NalaniFlynns/tiny-rmr-1-2.05/image/1.png

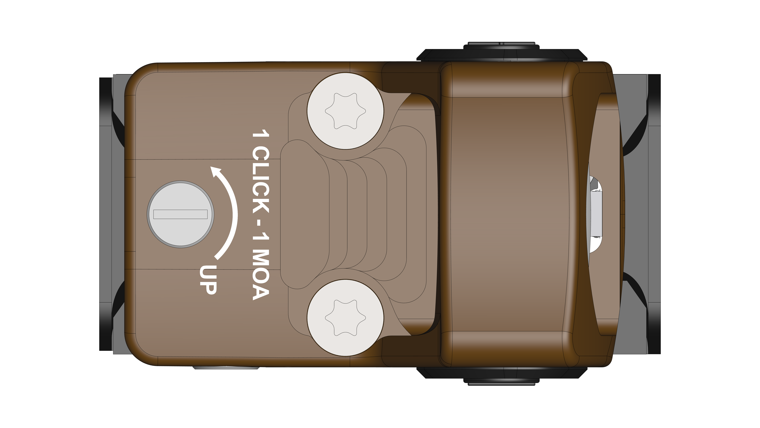
image/1.png
