NalaniFlynns/tiny-rmr-1-2.05/image/2.png

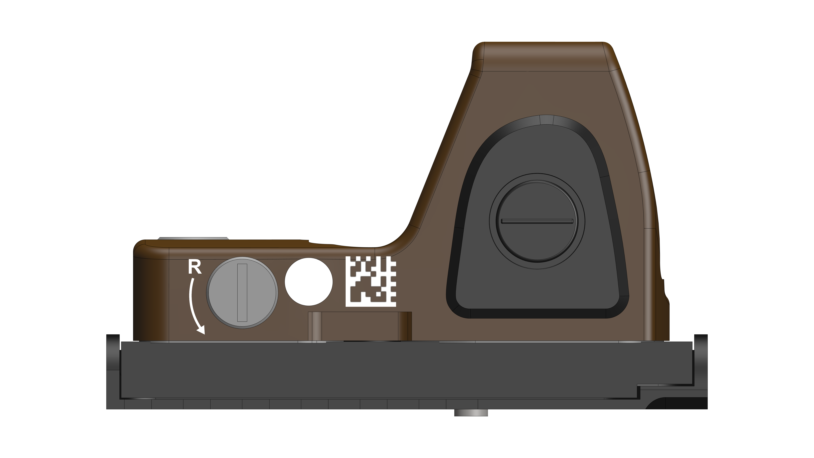
image/2.png
