NalaniFlynns/tiny-rmr-1-2.05/image/3.png

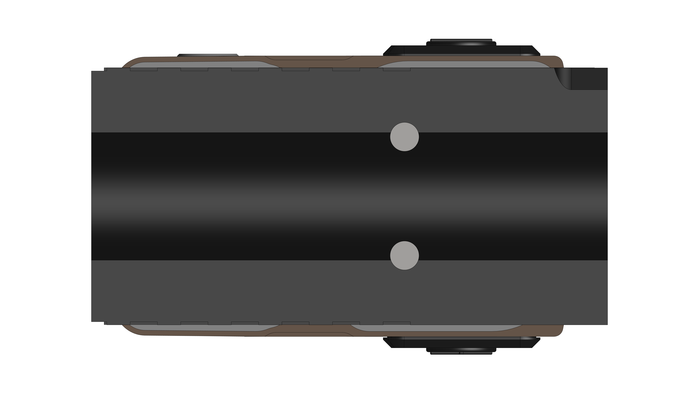
image/3.png
