NalaniFlynns/tiny-rmr-1-2.05/image/4.png

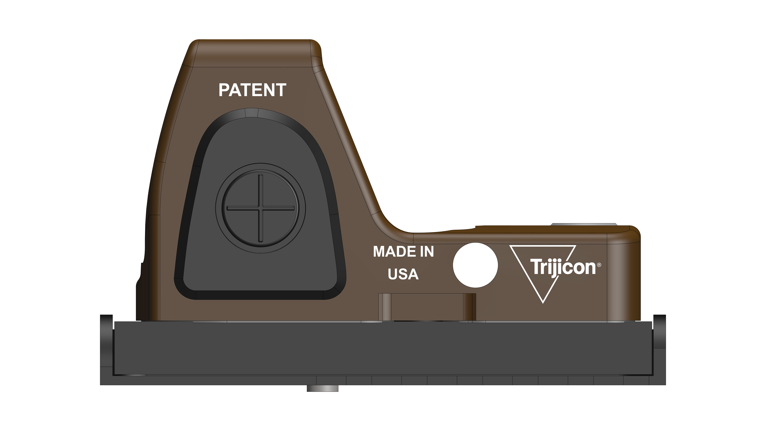
image/4.png
