NalaniFlynns/tiny-rmr-1-2.05/image/5.png

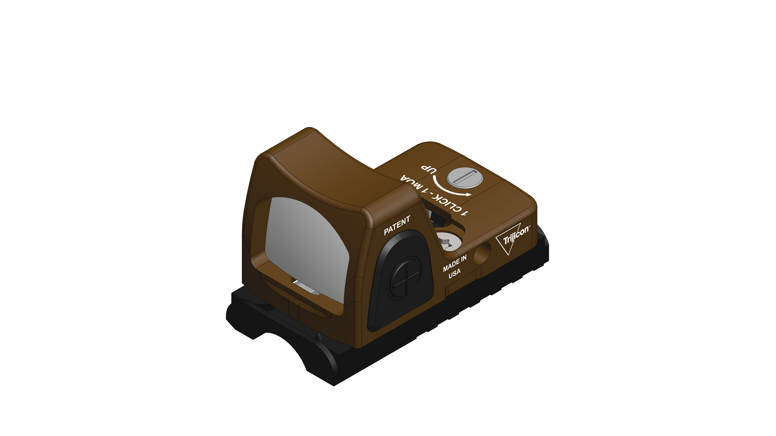
image/5.png
