NalaniFlynns/tiny-rmr-1-2.05/image/7.png

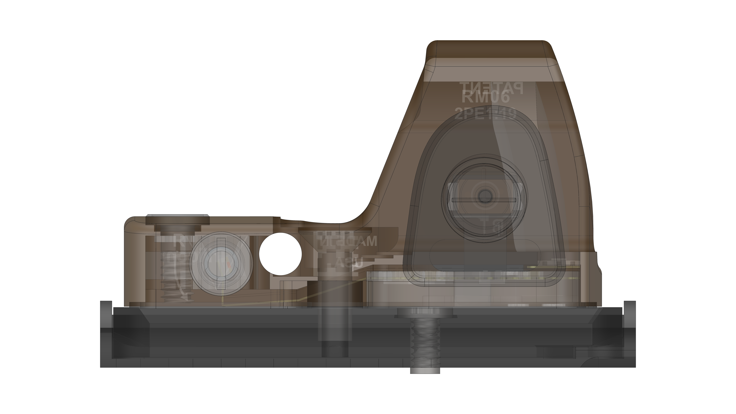
image/7.png
