NalaniFlynns/tiny-rmr-1-2.05/image/8.png

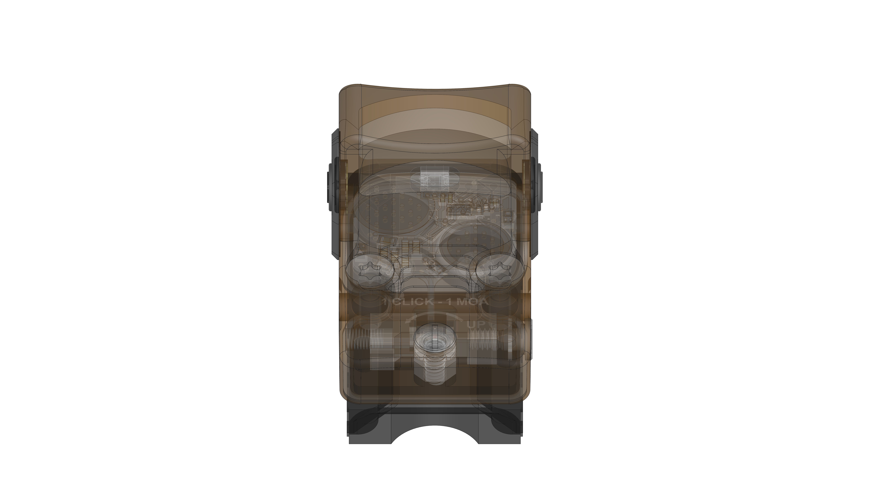
image/8.png
