NalaniFlynns/tiny-rmr-1-2.05/image/10.png

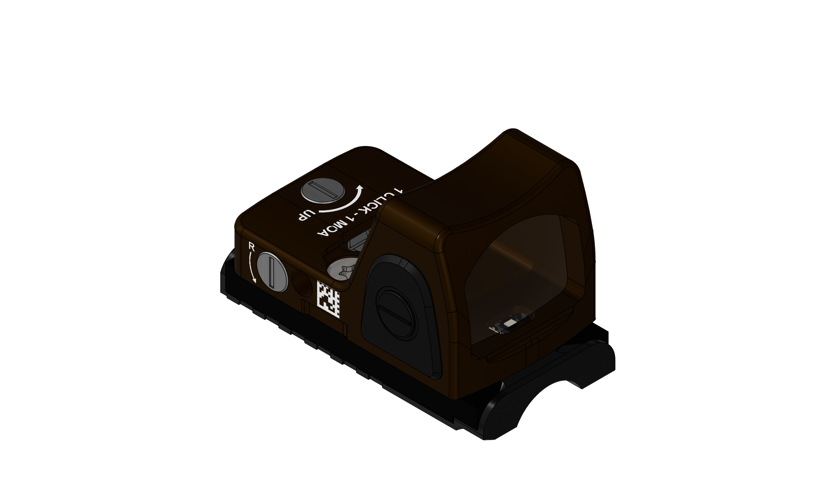
image/10.png
