NalaniFlynns/tiny-rmr-1-2.05/image/11.png

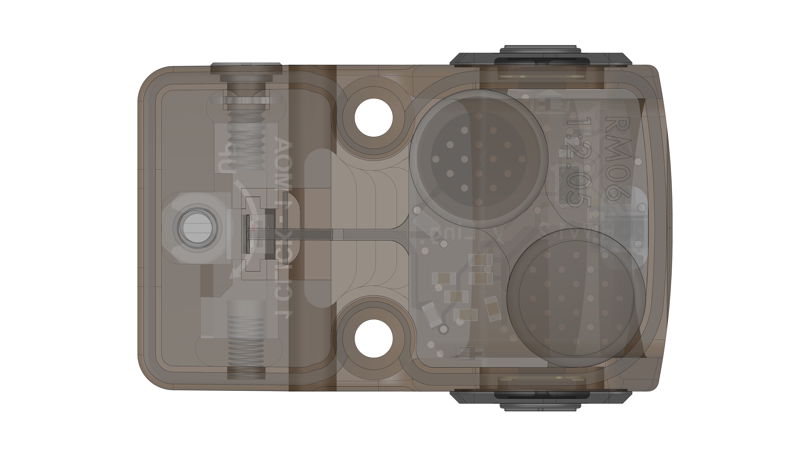
image/11.png
