NalaniFlynns/tiny-rmr-1-2.05/image/12.png

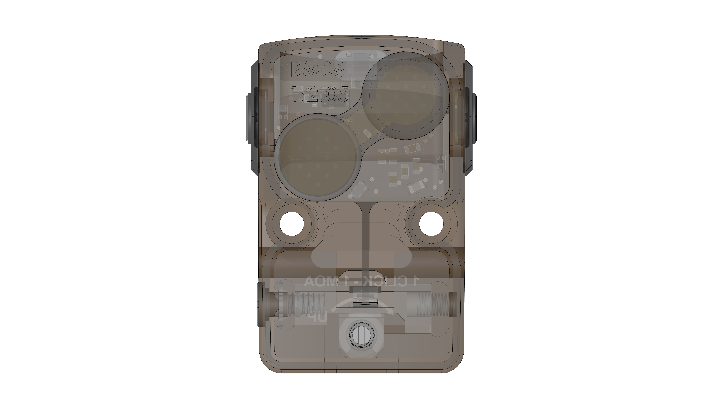
image/12.png
