NalaniFlynns/tiny-rmr-1-2.05/image/13.png

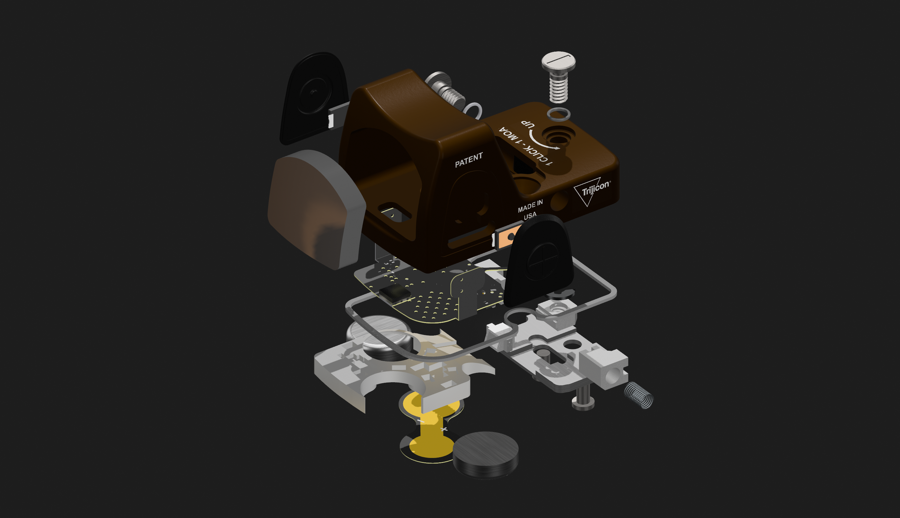
image/13.png
