NalaniFlynns/tiny-rmr-1-2.05/image/14.png

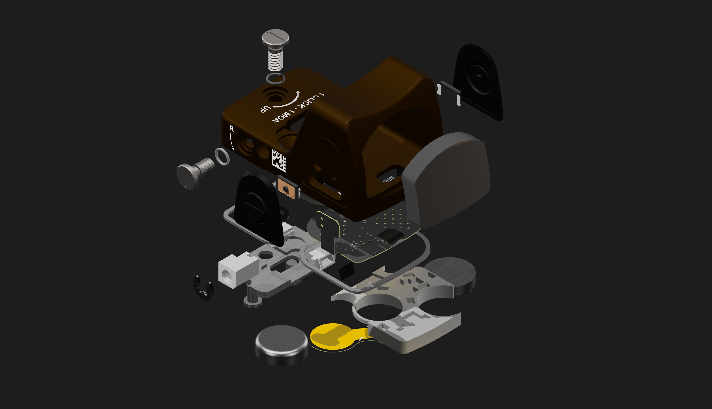
image/14.png
