NalaniFlynns/tiny-rmr-1-2.05/image/15.png

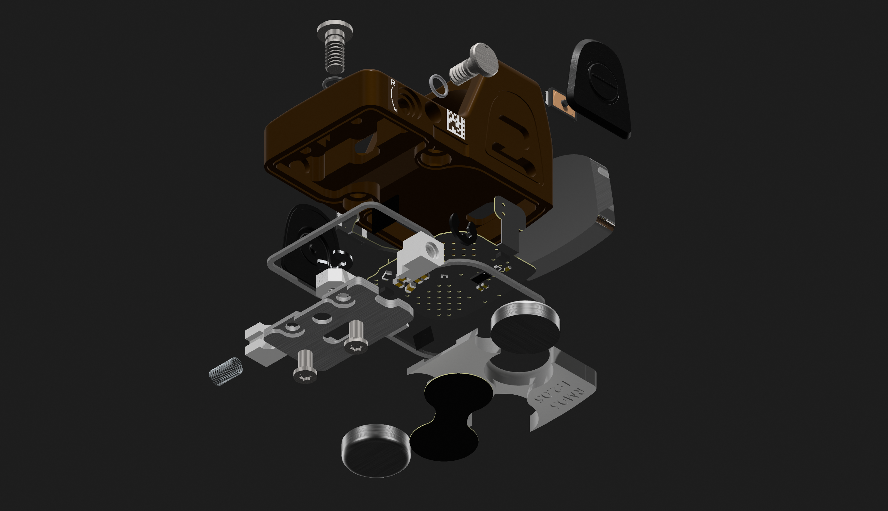
image/15.png
