NalaniFlynns/tiny-rmr-1-2.05/model/fix_step/螺丝占位_2.step

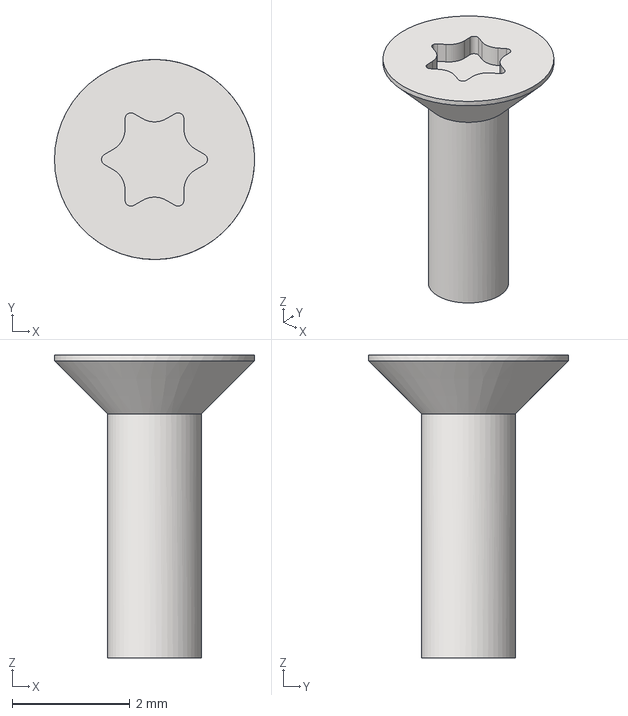
[picture p29: CAD file, 2026-08-04]
model/fix_step/螺丝占位_2.step
3.40 x 3.40 x 5.15 mm
