NalaniFlynns/tiny-rmr-1-2.05/model/fix_step/Y螺絲.step

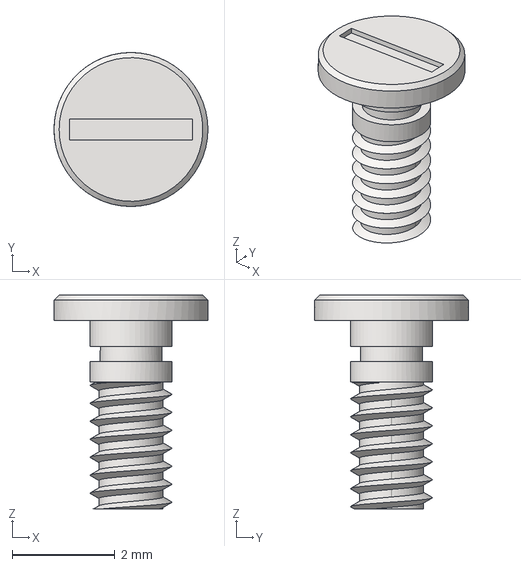
[picture p30: CAD file, 2026-08-04]
model/fix_step/Y螺絲.step
3.00 x 3.00 x 4.17 mm
