NalaniFlynns/tiny-rmr-1-2.05/model/fix_step/密封圈.step

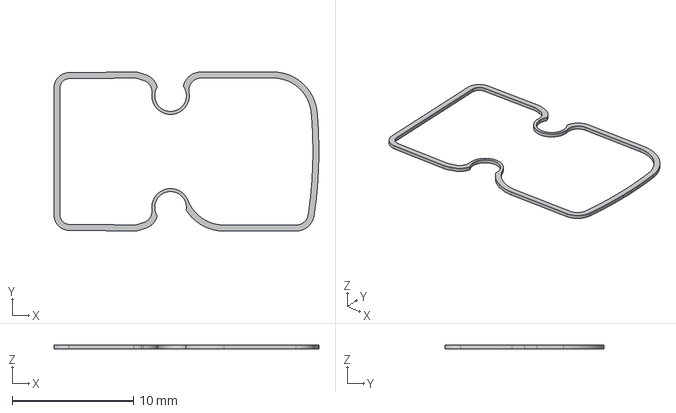
[picture p32: CAD file, 2026-08-04]
model/fix_step/密封圈.step
21.8 x 13.1 x 0.3 mm
