NalaniFlynns/tiny-rmr-1-2.05/model/fix_step/+.step

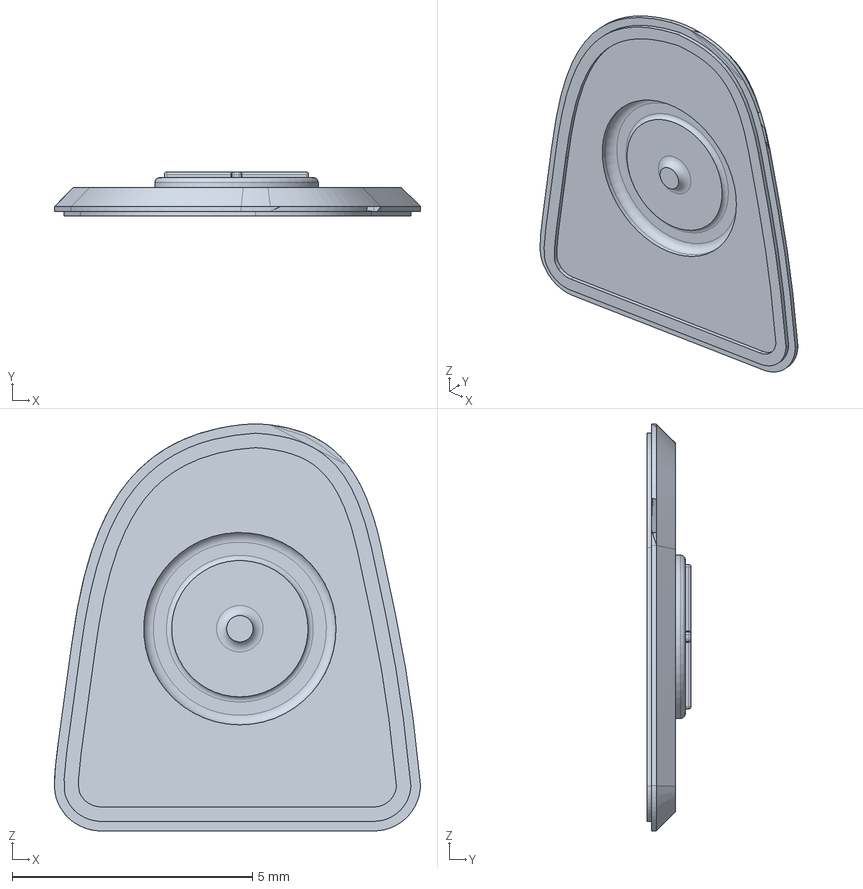
[picture p33: CAD file, 2026-08-04]
model/fix_step/+.step
7.61 x 0.92 x 8.47 mm
