NalaniFlynns/tiny-rmr-1-2.05/model/fix_step/FPC.step

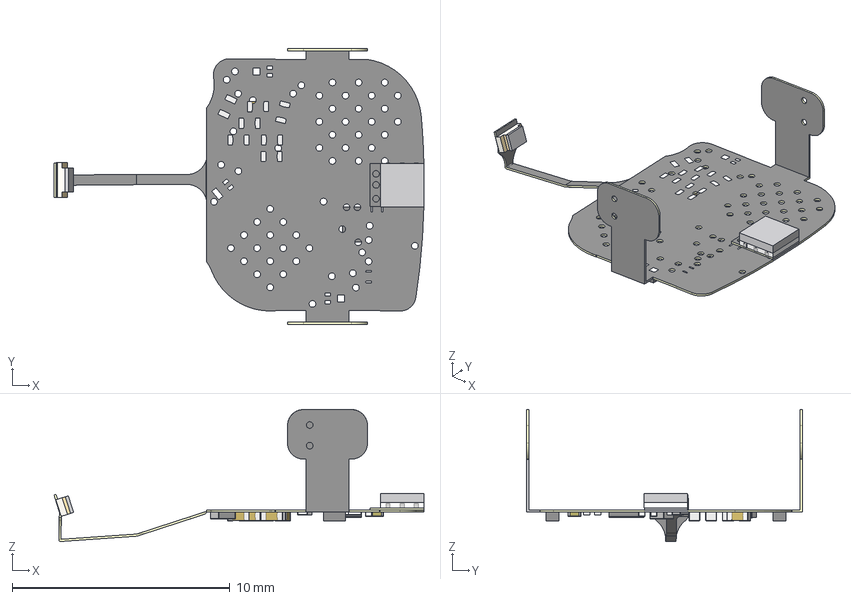
[picture p34: CAD file, 2026-08-04]
model/fix_step/FPC.step
17.0 x 12.6 x 6.06 mm
LED
Board~0xeg
R0402~R0402_L1.0-W0.5-H0.4~0xeg
C0402~C0402_L1.0-W0.5-H0.5~0xeg x 2
SOD-882_L1.0-W0.6-BI~WBFBP-03E_L1.0-W0.6-P0.64-BL~0xeg x 2
WSON-6_L2.0-W2.0-P0.65-BL-EP~WSON-6_L2.0-W2.0-H0.8-P0.65~0xeg
DSBGA-8_L1.6-W0.9-R2-C4-P0.35-TL~DSBGA-8_L1.6-W0.9-R2-C4-P0.35-TL~0xeg
X2-DFN1006-3_L1.0-W0.6-BR~X2-DFN1006-3_L1.0-W0.6-H0.4-BR~0xeg
R0201~R0201_L0.6-W0.3-H0.3~0xeg x 2
C0201~C0201_L0.6-W0.3-H0.3~0xeg x 3
