NalaniFlynns/tiny-rmr-1-2.05/model/fix_step/主動夾臂 (无螺纹-居中).step

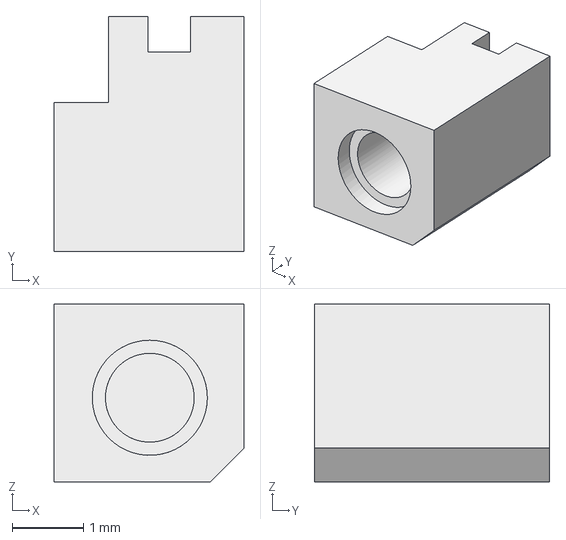
[picture p35: CAD file, 2026-08-04]
model/fix_step/主動夾臂 (无螺纹-居中).step
2.67 x 3.31 x 2.50 mm
