NalaniFlynns/tiny-rmr-1-2.05/model/fix_step/BTN_2.step

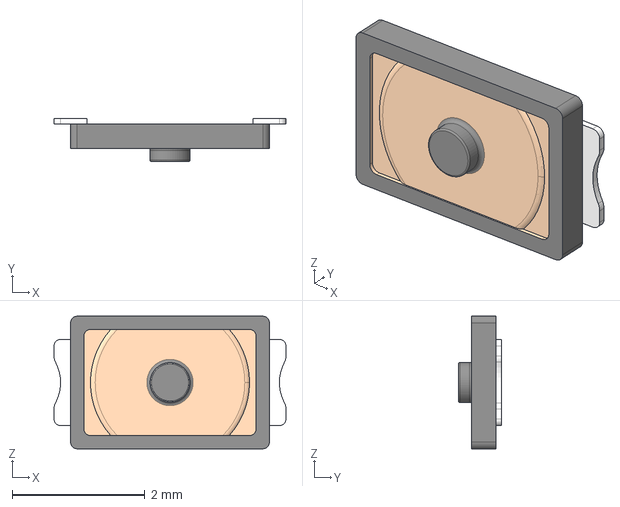
[picture p36: CAD file, 2026-08-04]
model/fix_step/BTN_2.step
3.50 x 0.65 x 2.00 mm
