NalaniFlynns/tiny-rmr-1-2.05/model/fix_step/主動夾臂 (偏置).step

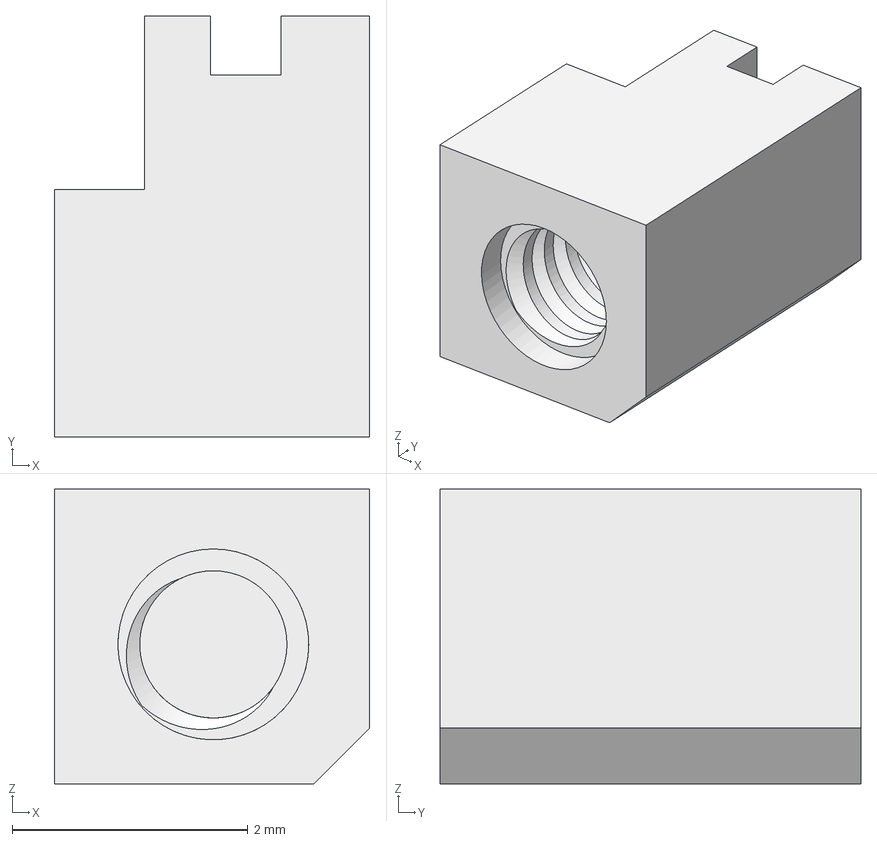
[picture p38: CAD file, 2026-08-04]
model/fix_step/主動夾臂 (偏置).step
2.67 x 3.57 x 2.50 mm
