NalaniFlynns/tiny-rmr-1-2.05/model/fix_step/彈簧.step

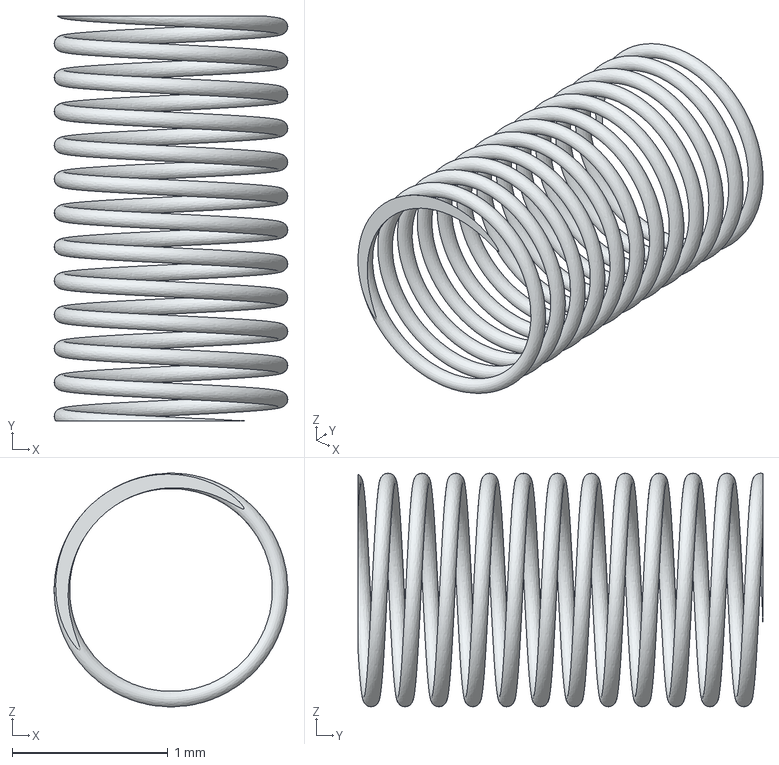
[picture p39: CAD file, 2026-08-04]
model/fix_step/彈簧.step
1.50 x 2.60 x 1.50 mm
