NalaniFlynns/tiny-rmr-1-2.05/model/fix_step/輔助夾臂 (偏置).step

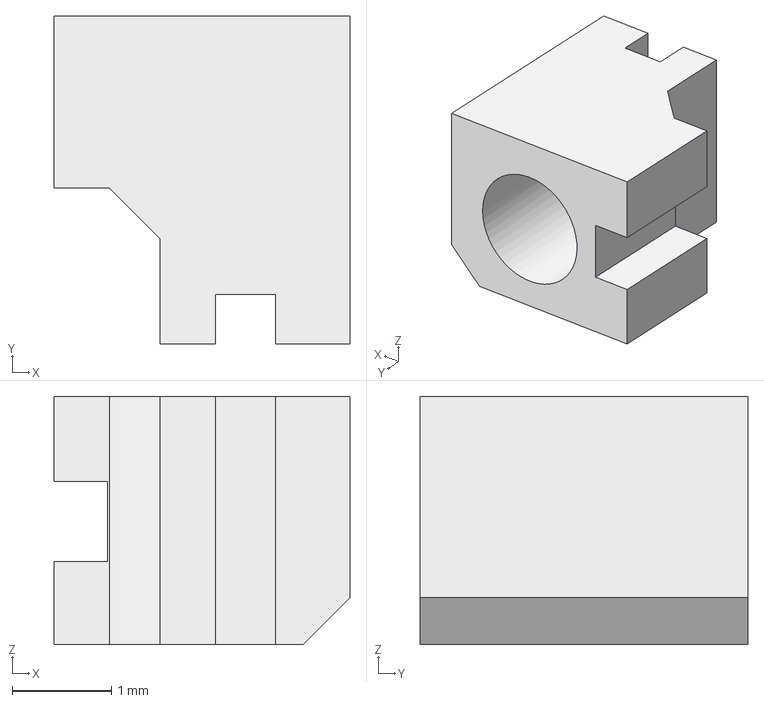
[picture p40: CAD file, 2026-08-04]
model/fix_step/輔助夾臂 (偏置).step
2.98 x 3.30 x 2.50 mm
