NalaniFlynns/tiny-rmr-1-2.05/model/fix_step/fpc-b.step

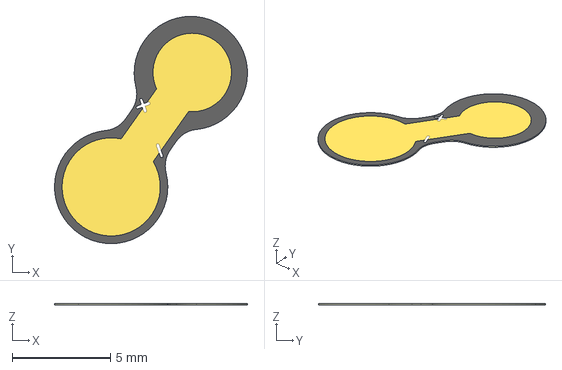
[picture p41: CAD file, 2026-08-04]
model/fix_step/fpc-b.step
9.83 x 11.6 x 0.09 mm
Board~aATq
TopSilkscreen~aATq x 2
