NalaniFlynns/tiny-rmr-1-2.05/model/fix_step/輔助夾臂.step

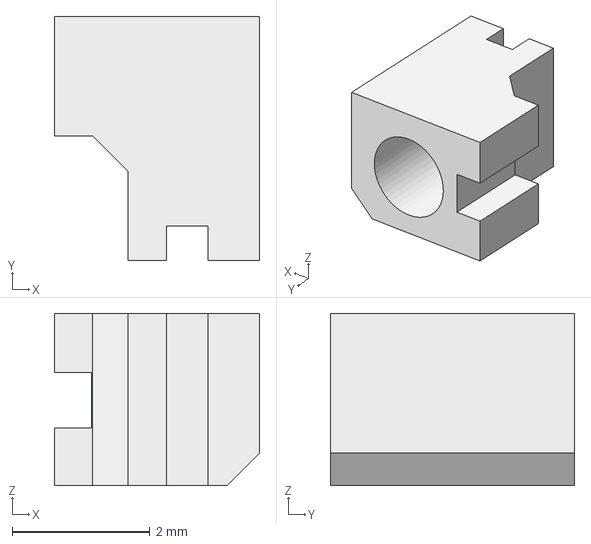
[picture p42: CAD file, 2026-08-04]
model/fix_step/輔助夾臂.step
2.98 x 3.54 x 2.50 mm
