NalaniFlynns/tiny-rmr-1-2.05/model/fix_step/结构盖板.step

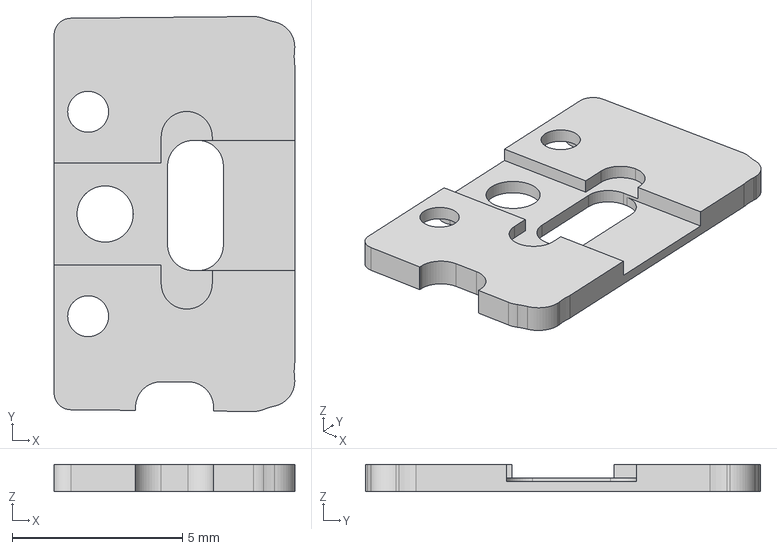
[picture p43: CAD file, 2026-08-04]
model/fix_step/结构盖板.step
7.07 x 11.6 x 0.8 mm
