NalaniFlynns/tiny-rmr-1-2.05/model/fix_step/X螺絲.step

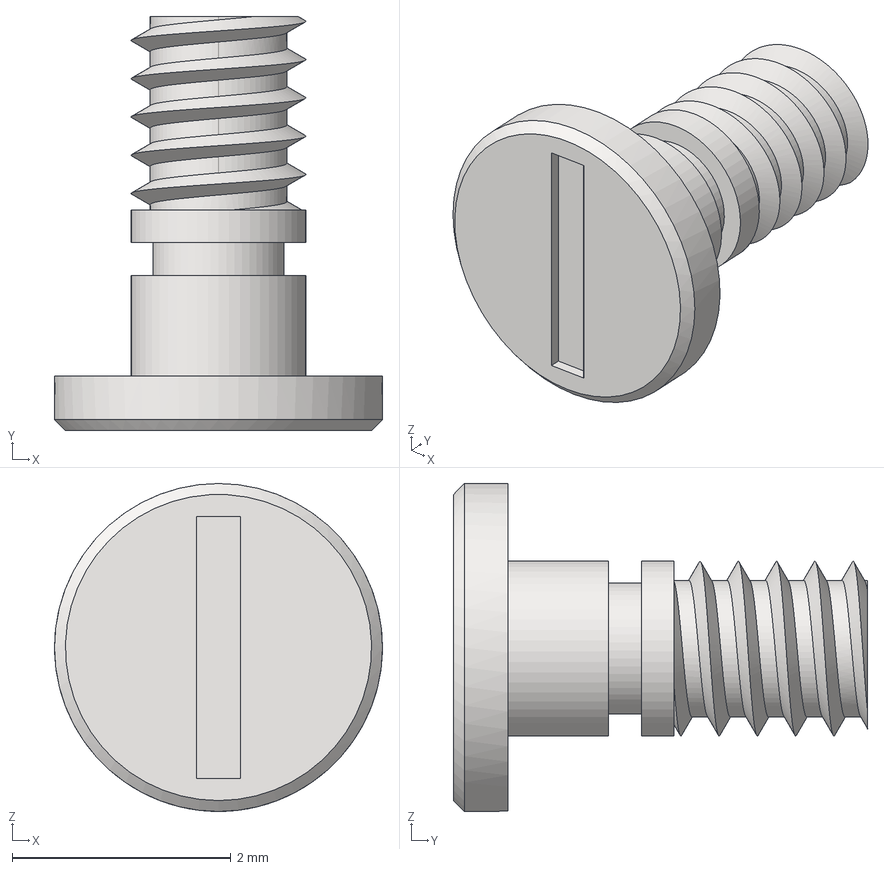
[picture p44: CAD file, 2026-08-04]
model/fix_step/X螺絲.step
3.00 x 3.79 x 3.00 mm
