NalaniFlynns/tiny-rmr-1-2.05/model/fix_step/載台.step

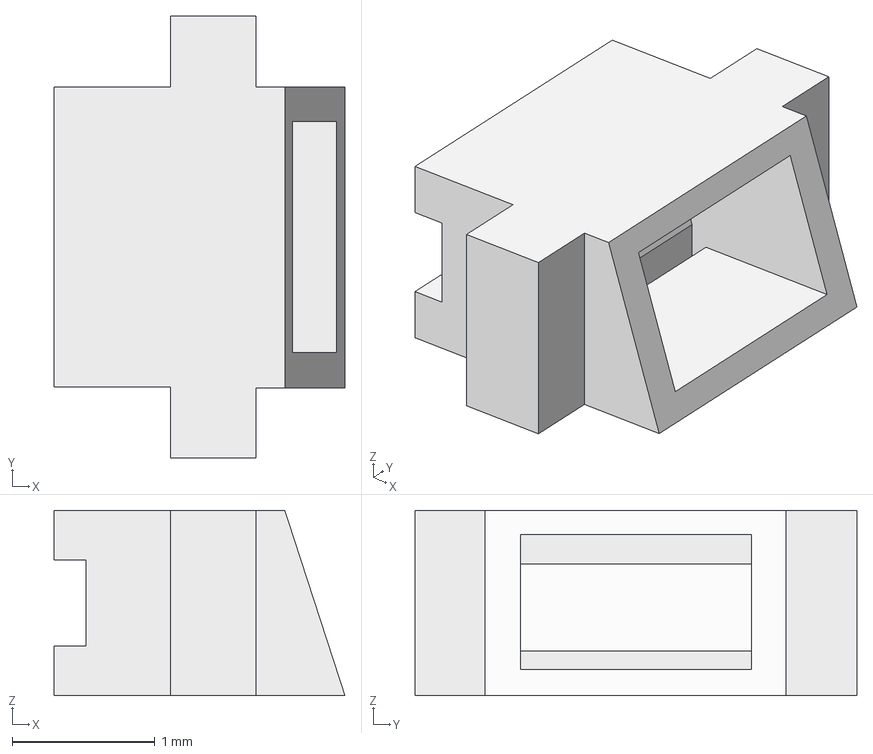
[picture p45: CAD file, 2026-08-04]
model/fix_step/載台.step
2.04 x 3.10 x 1.30 mm
