NalaniFlynns/tiny-rmr-1-2.05/model/fix_step/m1.2_2.step

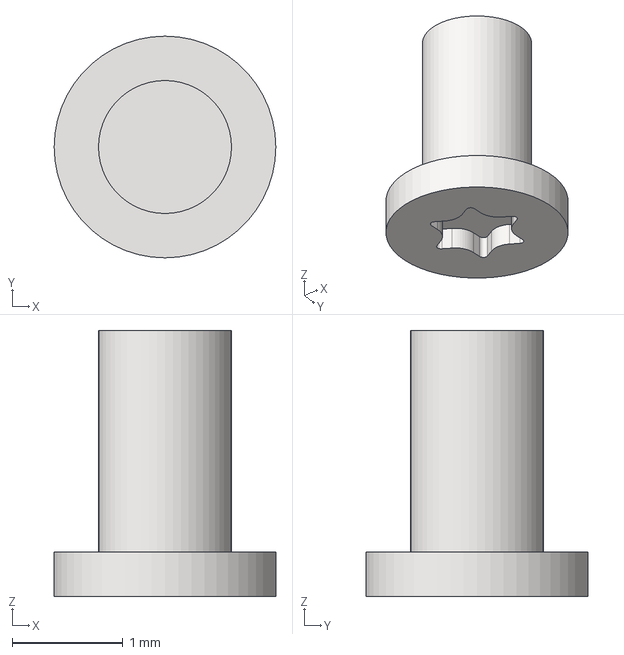
[picture p46: CAD file, 2026-08-04]
model/fix_step/m1.2_2.step
2.00 x 2.00 x 2.40 mm
