NalaniFlynns/tiny-rmr-1-2.05/model/fix_step/钢17转接板-左（无实体螺纹）.step

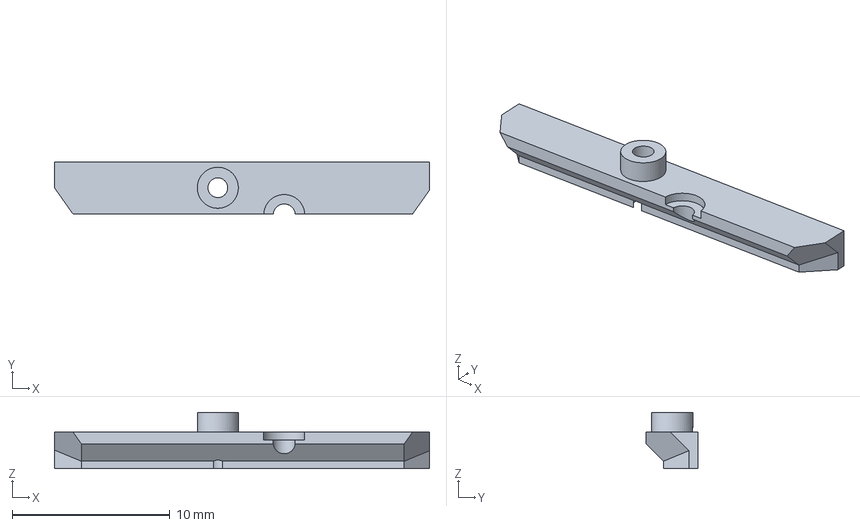
[picture p47: CAD file, 2026-08-04]
model/fix_step/钢17转接板-左（无实体螺纹）.step
23.8 x 3.28 x 3.58 mm
