NalaniFlynns/tiny-rmr-1-2.05/model/fix_step/從夾臂.step

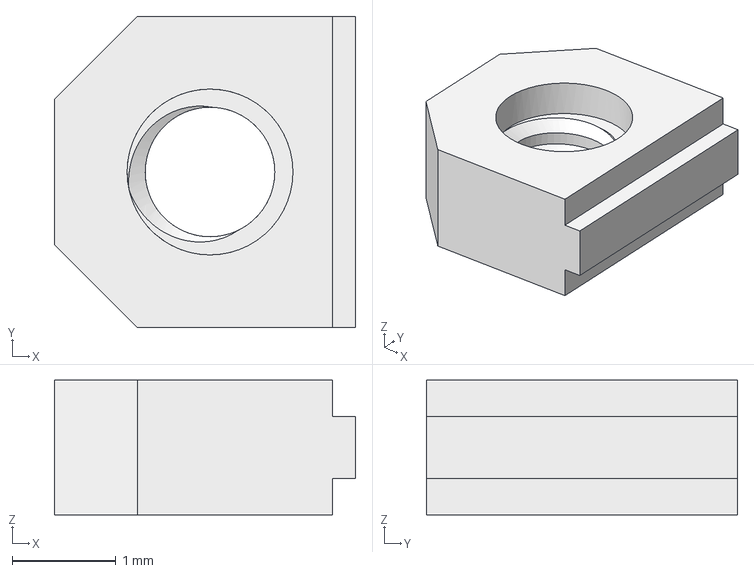
[picture p48: CAD file, 2026-08-04]
model/fix_step/從夾臂.step
2.90 x 3.00 x 1.30 mm
