NalaniFlynns/tiny-rmr-1-2.05/firmware/RMR/test_mailbox.c

#include "test_mailbox.h"
#include "app_config.h"
#include "nvm_flash.h"
#include "sys_battery.h"
#include "sys_led_pwm.h"
#include "sys_mode.h"
#include "hal_opt3001.h"
#include <ti/devices/msp/msp.h>

volatile Test_Mailbox_t g_test_box __attribute__((used)) = {
    .magic = 0, .version = 0x0100, .fw_version_str = FW_VERSION_STR
};

#if !POWER_SAVE_BUILD
static bool test_mode_active = false;
static uint32_t last_synced_params = 0;   /* guard vs host cfg_params writes (race fix) */
#endif

#if !POWER_SAVE_BUILD
static void test_box_sync_cfg(void) {
    g_test_box.cfg_params = sys_memory.params;
    g_test_box.cfg_features = sys_memory.features;
    g_test_box.cfg_r_base = sys_memory.r_base;
    g_test_box.cfg_r_series = sys_memory.r_series;
    g_test_box.cfg_v_led_fw = sys_memory.v_led_fw;
    g_test_box.cfg_i_max_ua = sys_memory.i_max_ua;
    g_test_box.cfg_batt_p_uw = sys_memory.batt_p_uw;
    g_test_box.cfg_als_min_brt = sys_memory.als_min_brt;
    g_test_box.cfg_lvp_crit = sys_memory.lvp_crit;
    g_test_box.cfg_lvp_ext = sys_memory.lvp_ext;
    g_test_box.cfg_als_sqrt_factor = sys_memory.als_sqrt_factor;
    g_test_box.cfg_als_cap_low_x100 = sys_memory.als_cap_low_x100;
    g_test_box.cfg_als_cap_high_x100 = sys_memory.als_cap_high_x100;
    /* sync 后更新守卫值, 避免 cfg_params 镜像冻结 (race fix 补完) */
    last_synced_params = g_test_box.cfg_params;
}
#endif
void test_mailbox_task(void) {
#if POWER_SAVE_BUILD
    /* 省电版: 常态不刷 mailbox 省电; FLASH_MODE 是量产唯一调试通道, 刷最小遥测供 RMRDebugger 显示 */
    if (sys_state == SYS_FLASH_MODE) {
        g_test_box.vbatt_mv = g_vbatt_mv_filtered;
        g_test_box.vbatt_raw_mv = g_vbatt_mv_raw;
        g_test_box.sys_state_mirror = sys_state;
        g_test_box.rst_cause = (uint8_t)g_rst_cause;
        g_test_box.sys_clk_khz = 24000u;
        g_test_box.current_level = sys_memory.params & 0xFF;
        g_test_box.current_brt_val = g_current_brt;
        g_test_box.current_pwm_val = g_last_applied_pwm;
        g_test_box.state_inactivity_sec = g_inactivity_sec;
        g_test_box.nvm_is_dirty = nvm_is_dirty() ? 1 : 0;
        g_test_box.nvm_save_fail_cnt = nvm_get_save_fail_cnt();
        g_test_box.raw_key_minus = ((DL_GPIO_readPins(PORT_BTN, PIN_BT1) & PIN_BT1) == 0) ? 1 : 0;
        g_test_box.raw_key_plus  = ((DL_GPIO_readPins(PORT_BTN, PIN_BT2) & PIN_BT2) == 0) ? 1 : 0;
    }
#else
    /* 冷/热启动都清一次调试授权/覆盖: .data 在热复位后保留旧值, 残留 magic 会把设备锁在 TEST_MODE 绕过自动关机;
       调试器在用户操作时会重新写入授权, 读取遥测不受影响 */
    static bool auth_cleared_at_boot = false;
    if (!auth_cleared_at_boot) {
        auth_cleared_at_boot = true;
        test_box_exit_test_mode();
    }

    bool auth_ok = (g_test_box.magic == TEST_MAGIC && g_test_box.host_version == g_test_box.version);

            /* per-tick sync: skip when host wrote cfg_params (write-config race fix): */
    if (g_test_box.cfg_params == last_synced_params) {
        g_test_box.cfg_params = sys_memory.params;
        last_synced_params = g_test_box.cfg_params;
    }   /* 每 tick 同步, 让调试器实时显示档位/ALS偏移变化 */
        /* ===== 实时监视器刷新(每 tick) ===== */
    g_test_box.vbatt_mv = g_vbatt_mv_filtered;
    g_test_box.vbatt_raw_mv = g_vbatt_mv_raw;
    g_test_box.sys_state_mirror = sys_state;
    g_test_box.rst_cause = (uint8_t)g_rst_cause;
    g_test_box.sys_clk_khz = 24000u;   /* MSPM0C110x SYSOSC 恒定 24MHz(4M 写无效), 真实 tick=1ms */
    g_test_box.cfg_params = sys_memory.params;   /* 每 tick 同步, 让调试器实时显示挡位/ALS偏移变化 */
    g_test_box.current_level = sys_memory.params & 0xFF;
    g_test_box.current_brt_val = g_current_brt; 
    g_test_box.current_pwm_val = g_last_applied_pwm; 
    g_test_box.est_i_peak_ua = g_est_i_peak_ua;
        /* 平均电流 = 实测峰值电流 × 实际 PWM 占空比(0..1000‰), 反映真实负载而非设定值 */
    uint32_t duty_mille = ((uint32_t)(PWM_REG_MAX - g_last_applied_pwm) * 1000u) / (uint32_t)PWM_REG_MAX;
    g_test_box.est_i_avg_ua = (uint32_t)(((uint64_t)g_est_i_peak_ua * duty_mille) / 1000u);
    g_test_box.est_v_led_mv = sys_memory.v_led_fw;
    g_test_box.est_p_led_uw = (uint32_t)(((uint64_t)sys_memory.v_led_fw * g_test_box.est_i_avg_ua) / 1000ULL);
    g_test_box.est_hw_power_uw = (uint32_t)(((uint64_t)g_vbatt_mv_raw * g_test_box.est_i_avg_ua) / 1000ULL);
    g_test_box.dyn_r_mohm = g_dyn_r_mohm;
    g_test_box.safe_brt_out = g_safe_brt_out;
    g_test_box.limit_i_led = g_limit_i_led;
    g_test_box.limit_v_drop = g_limit_v_drop;
    g_test_box.limit_i_brt = g_limit_i_brt;
    g_test_box.limit_p_avg = g_limit_p_avg;
    g_test_box.als_lux_raw = g_als_lux_raw;
    g_test_box.als_lux_filtered = g_als_lux_filtered;
    g_test_box.als_err_cnt = g_als_err_cnt;
    g_test_box.sensor_status = g_als_sensor_status;
    g_test_box.raw_key_minus = ((DL_GPIO_readPins(PORT_BTN, PIN_BT1) & PIN_BT1) == 0) ? 1 : 0;
    g_test_box.raw_key_plus  = ((DL_GPIO_readPins(PORT_BTN, PIN_BT2) & PIN_BT2) == 0) ? 1 : 0;
    g_test_box.state_is_dimmed = g_is_dimmed ? 1 : 0;
    g_test_box.state_is_overshot = g_is_overshot ? 1 : 0;
    g_test_box.state_debug_mode = (sys_memory.features & FLAG_SWD_IN_OFF_STATE) ? 1 : 0;
    g_test_box.nvm_is_dirty = nvm_is_dirty() ? 1 : 0;
    g_test_box.nvm_save_fail_cnt = nvm_get_save_fail_cnt();
    g_test_box.state_inactivity_sec = g_inactivity_sec;
    g_test_box.nvm_seq_id = sys_memory.seq_id;
    g_test_box.nvm_sector_addr = nvm_get_sector_addr();
    g_test_box.nvm_slot_idx = nvm_get_slot_idx();

    if (auth_ok && sys_state != SYS_TEST_MODE && sys_state != SYS_OFF) {
        test_mode_active = true;
        sys_state = SYS_TEST_MODE;
        g_inactivity_sec = 0;   /* 进入调试态视为用户在场, 重新计时 */
        g_is_dimmed = false;
        opt3001_init();
        g_test_box.cfg_params = sys_memory.params;
        g_test_box.cfg_features = sys_memory.features;
        g_test_box.cfg_r_base = sys_memory.r_base;
        g_test_box.cfg_r_series = sys_memory.r_series;
        g_test_box.cfg_v_led_fw = sys_memory.v_led_fw;
        g_test_box.cfg_i_max_ua = sys_memory.i_max_ua;
        g_test_box.cfg_batt_p_uw = sys_memory.batt_p_uw;
        g_test_box.cfg_als_min_brt = sys_memory.als_min_brt;
        g_test_box.cfg_lvp_crit = sys_memory.lvp_crit;
        g_test_box.cfg_lvp_ext = sys_memory.lvp_ext;
        g_test_box.cfg_als_sqrt_factor = sys_memory.als_sqrt_factor;
        g_test_box.cfg_als_cap_low_x100 = sys_memory.als_cap_low_x100;
        g_test_box.cfg_als_cap_high_x100 = sys_memory.als_cap_high_x100;
        g_test_box.status = TEST_ST_IDLE;
        g_test_box.cmd_ack = 0;
        /* ???????????, ?? ovr_brt_val=0 ???????? */
        if (g_test_box.ovr_led_mode == 0 && g_test_box.ovr_brt_val == 0 && g_current_brt > 0) {
            g_test_box.ovr_brt_val = g_current_brt;
        }
    } else if (!auth_ok && sys_state == SYS_TEST_MODE) {
        NVIC_SystemReset();   /* 授权丢失 -> 复位 */
    }

    if (sys_state == SYS_TEST_MODE && g_test_box.cmd != 0) {
        g_inactivity_sec = 0;   /* 主机下发命令视为用户在场 */
        g_is_dimmed = false;
        uint32_t c = g_test_box.cmd;
        g_test_box.status = TEST_ST_BUSY;
        g_test_box.cmd = 0;
        if (c == 2) {
            NVIC_SystemReset();
        } else if (c == 3) {   /* 写配置(mask 过滤) */
            sys_memory.params = g_test_box.cfg_params;
            sys_memory.features = g_test_box.cfg_features & FEATURE_RUNTIME_MASK;
            sys_memory.r_base = g_test_box.cfg_r_base;
            sys_memory.r_series = g_test_box.cfg_r_series;
            sys_memory.v_led_fw = g_test_box.cfg_v_led_fw;
            sys_memory.i_max_ua = g_test_box.cfg_i_max_ua;
            sys_memory.batt_p_uw = g_test_box.cfg_batt_p_uw;
            sys_memory.als_min_brt = g_test_box.cfg_als_min_brt;
            sys_memory.lvp_crit = g_test_box.cfg_lvp_crit;
            sys_memory.lvp_ext = g_test_box.cfg_lvp_ext;
            /* ALS ????: 1..20, 0 ????????? */
            sys_memory.als_sqrt_factor = (g_test_box.cfg_als_sqrt_factor > 20) ? 20 : g_test_box.cfg_als_sqrt_factor;
            sys_memory.als_cap_low_x100 = (g_test_box.cfg_als_cap_low_x100 > 20) ? 20 : g_test_box.cfg_als_cap_low_x100;
            sys_memory.als_cap_high_x100 = (g_test_box.cfg_als_cap_high_x100 > 20) ? 20 : g_test_box.cfg_als_cap_high_x100;
            g_test_box.status = TEST_ST_OK;  test_box_sync_cfg();  /* 同步镜像, 供 GUI 读回 */
        } else if (c == 4) {   /* 保存 */
            nvm_mark_dirty();
            if (nvm_save_dirty()) g_test_box.status = TEST_ST_OK;
            else g_test_box.status = TEST_ST_ERR_FLASH;
            test_box_sync_cfg();  /* 保存后同步镜像, 供 GUI 读回 */
        } else if (c == 5) {   /* 恢复出厂 + 保存 */
            nvm_force_factory_reset();
            if (nvm_save_dirty()) g_test_box.status = TEST_ST_OK;
            else g_test_box.status = TEST_ST_ERR_FLASH;
            test_box_sync_cfg();  /* 保存后同步镜像, 供 GUI 读回 */
        } else if (c == 6) {   /* 开机(测压达标)并退出测试模式 */
            bool power_on = true;
            if (sys_state == SYS_OFF) {
                power_on = battery_startup_check();
                if (power_on) {
                    sys_state = SYS_RUN;
                    g_inactivity_sec = 0;
                    g_is_dimmed = false;
                    g_test_box.boot_refuse_reason = BOOT_REFUSE_NONE;
                    mode_init();
                } else {
                    g_test_box.boot_refuse_reason = BOOT_REFUSE_VOLT;
                }
            } else {
                sys_state = SYS_RUN;   /* 已在运行/测试态: 直接保持运行 */
                mode_init();           /* TEST->RUN 也需重新初始化 ALS/档位标志 */
            }
            test_mode_active = false;
            g_test_box.magic = 0;   /* 退出测试模式, 保持 RUN */
            g_test_box.ovr_led_mode = 0;
            g_test_box.ovr_key_minus = 0;
            g_test_box.ovr_key_plus = 0;
            g_test_box.ovr_als_en = 0;
            g_test_box.ovr_block_phys_keys = 0;
            g_test_box.status = power_on ? TEST_ST_OK : TEST_ST_ERR_INV_CMD;
        } else if (c == 7) {   /* 关机并退出测试模式 */
            if (sys_state != SYS_OFF) {
                sys_state = SYS_OFF;
                nvm_mark_dirty();
                nvm_save_dirty();
            }
            test_mode_active = false;
            g_test_box.magic = 0;
            g_test_box.ovr_led_mode = 0;
            g_test_box.ovr_key_minus = 0;
            g_test_box.ovr_key_plus = 0;
            g_test_box.ovr_als_en = 0;
            g_test_box.ovr_block_phys_keys = 0;
        } else if (c == 8) {   /* factory reset: user config only, keep calibration */
            nvm_reset_user_config();
            if (nvm_save_dirty()) g_test_box.status = TEST_ST_OK;
            else g_test_box.status = TEST_ST_ERR_FLASH;
            test_box_sync_cfg();  /* sync mirror after reset, for GUI readback */
            g_test_box.status = TEST_ST_OK;
        } else {
            g_test_box.status = TEST_ST_ERR_INV_CMD;
        }
        g_test_box.cmd_ack = c;
    }

    /* 测试态: 每 tick 刷新诊断计算数据 */
    if (sys_state == SYS_TEST_MODE) {
        battery_get_safe_brt(BRT_SCALE_MAX);
    }

    /* 正常退出测试模式 -> SYS_FLASH_MODE */
    if (test_mode_active && sys_state != SYS_TEST_MODE && sys_state != SYS_OFF) {
        test_mode_active = false;
        sys_state = SYS_FLASH_MODE;
        g_test_box.ovr_led_mode = 0;
        g_test_box.ovr_key_minus = 0;
        g_test_box.ovr_key_plus = 0;
        g_test_box.ovr_als_en = 0;
        g_test_box.ovr_block_phys_keys = 0;
        g_test_box.cmd_ack = 0;
    }
#endif
}

#if !POWER_SAVE_BUILD
/* 强制退出测试态: 清授权/覆盖/本地标志, 防止残留 magic 复活 TEST_MODE */
void test_box_exit_test_mode(void) {
    test_mode_active = false;
    g_test_box.magic = 0;
    g_test_box.host_version = 0;
    g_test_box.cmd = 0;
    g_test_box.cmd_ack = 0;
    g_test_box.ovr_led_mode = 0;
    g_test_box.ovr_key_minus = 0;
    g_test_box.ovr_key_plus = 0;
    g_test_box.ovr_als_en = 0;
    g_test_box.ovr_block_phys_keys = 0;
    g_test_box.ovr_brt_val = 0;
    g_test_box.ovr_pwm_val = 0;
    g_test_box.ovr_als_lux = 0;
}
#else
void test_box_exit_test_mode(void) {}
#endif
